4x1md/phone_rtty_interface/docs/images/oscillograms/osc_004.png

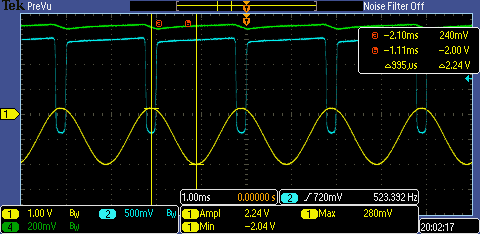
docs/images/oscillograms/osc_004.png
