4x1md/phone_rtty_interface/docs/images/oscillograms/osc_006.png

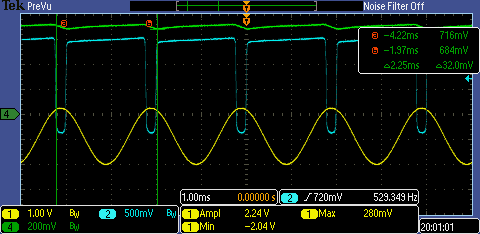
docs/images/oscillograms/osc_006.png
