4x1md/phone_rtty_interface/docs/images/qsl.jpg

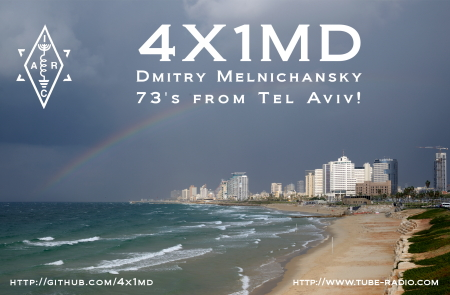
docs/images/qsl.jpg
