4x1md/phone_rtty_interface/docs/images/s7_mid_volume.png

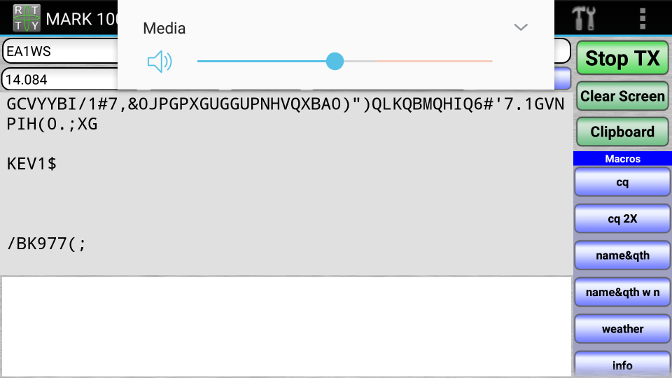
docs/images/s7_mid_volume.png
