4x1md/phone_rtty_interface/docs/schematics_a4/phone_rtty_bjt_a4.png

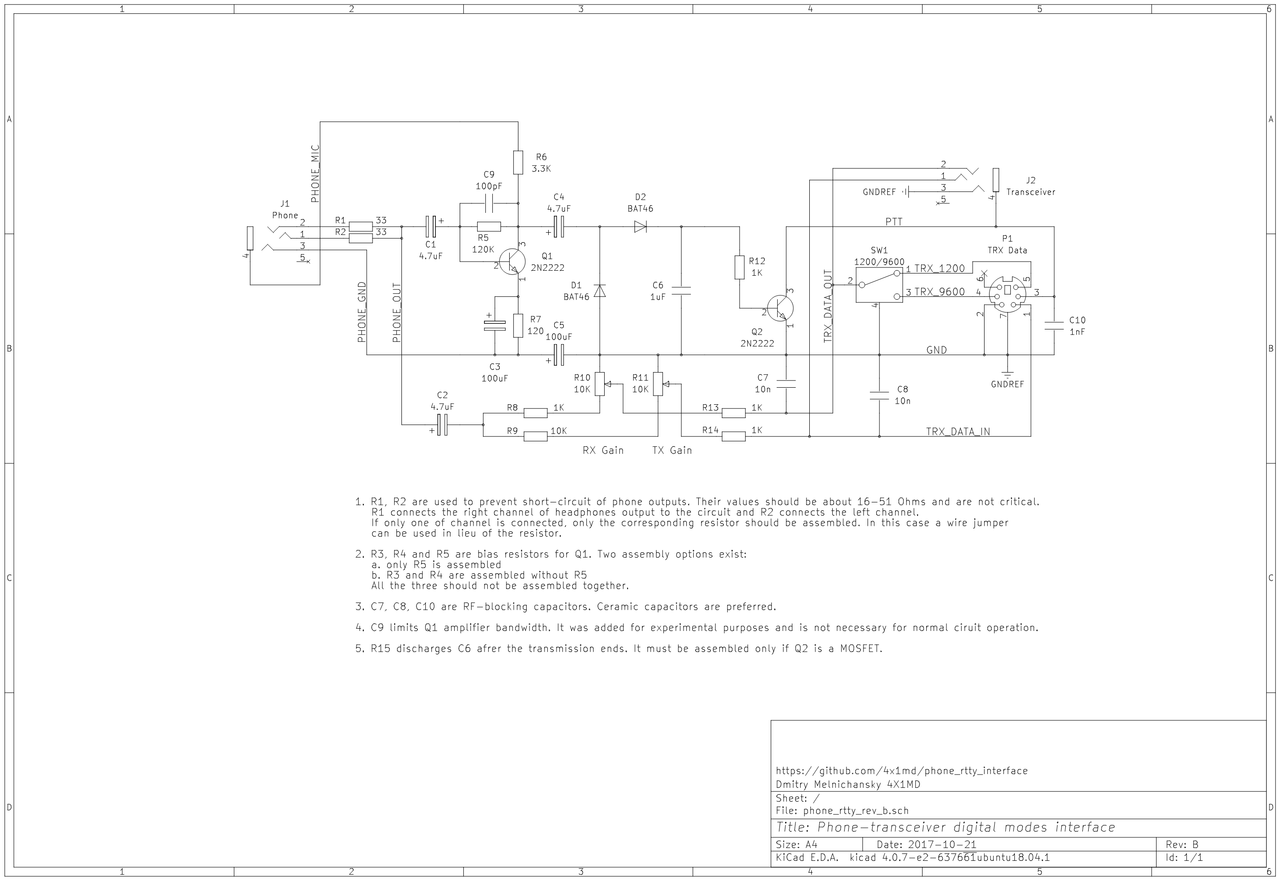
docs/schematics_a4/phone_rtty_bjt_a4.png
