4x1md/phone_rtty_interface/ltspice/rtty_interface_bjt.asc

C1: cap; 4.7µ; V=10 Irms=9.29 Rser=0.00646575 Lser=0 mfg="KEMET" pn="C0603C475K8PAC" type="X5R"
C2: polcap; 100µ; V=6.3 Irms=0 Rser=0.9 Lser=0 mfg="AVX" pn="TAJD107M006" type="Tantalum"
C3: cap; 4.7µ; V=10 Irms=9.29 Rser=0.00646575 Lser=0 mfg="KEMET" pn="C0603C475K8PAC" type="X5R"
C4: cap; 0.1µ; V=10 Irms=728m Rser=0.14361 Lser=0 mfg="KEMET" pn="C0603C104K8RAC" type="X7R"
C5: cap; 0.001µ; V=10 Irms=40.9m Rser=5.11126 Lser=0 mfg="KEMET" pn="C0603C102K8RAC" type="X7R"
D1: schottky; BAT54
D2: schottky; BAT54
Q1: npn; 2N2222
Q2: npn; 2N2222
R1: EuropeanResistor; 121K; tol=1 pwr=0.1
R2: EuropeanResistor; 3.32K; tol=1 pwr=0.1
R3: EuropeanResistor; 121; tol=1 pwr=0.1
R5: EuropeanResistor; {Rbase}; tol=1 pwr=0.1
Rpull: EuropeanResistor; 11K; tol=1 pwr=0.1
Rs: EuropeanResistor; 2.33K
V1: voltage; 2.8V
V2: voltage; SINE(0 2.2 250 0.25)
V3: voltage; 5.0V
Named nets: 0, Vcc, IN, PTT, collector, rect, base
.tran 400ms startup
.step param Rbase list 1K 4.7K 10K
FT-817
Phone
Microphone input
Headphones output
PTT circuit
